sandgum/Triangulate-SF_01-Speaker-Frame/CAD/SF_01 Speaker Frame_STEP/Wall Mounting Piece.step

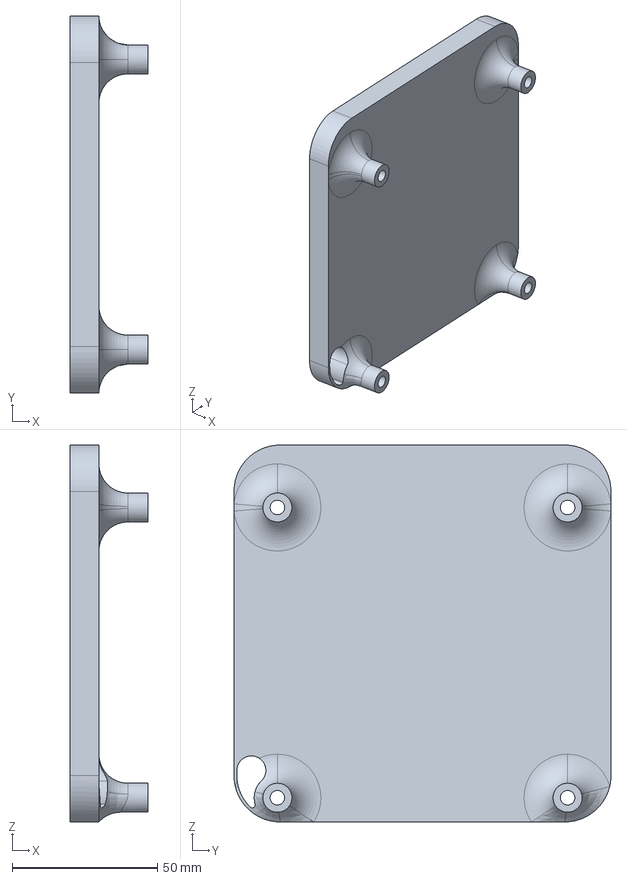
[picture p15: CAD file, 2026-06-28]
CAD/SF_01 Speaker Frame_STEP/Wall Mounting Piece.step
26.9 x 129.9 x 129.9 mm
