sandgum/Triangulate-SF_01-Speaker-Frame/PCB V1.1/PCB Components/TPS54540DDAR Model by Texas Instruments/TPS54540DDAR.step

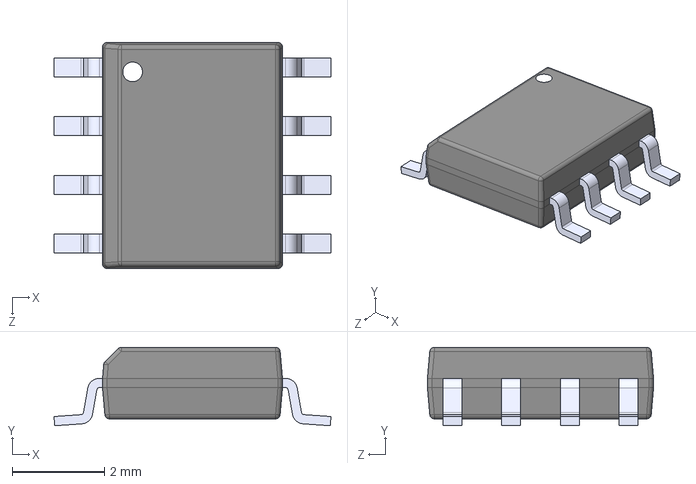
[picture p16: CAD file, 2026-08-03]
PCB V1.1/PCB Components/TPS54540DDAR Model by Texas Instruments/TPS54540DDAR.step
6.00 x 1.70 x 4.90 mm
