sandgum/Triangulate-SF_01-Speaker-Frame/PCB V1.1/PCB Components/JS202011JCQN 3D Model STEP 1.STEP

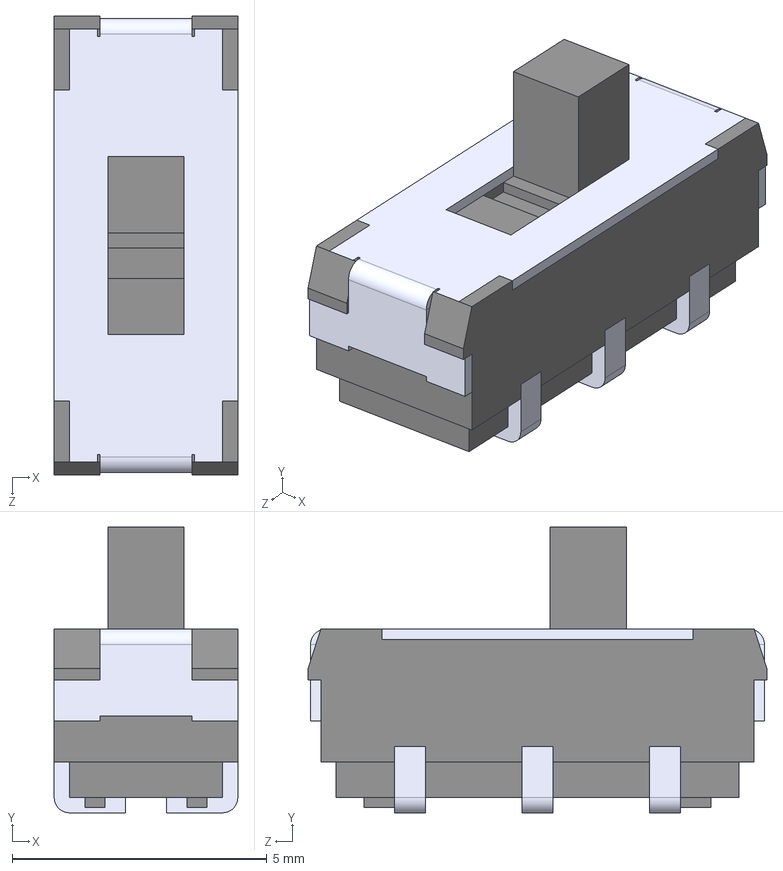
[picture p17: CAD file, 2026-06-28]
PCB V1.1/PCB Components/JS202011JCQN 3D Model STEP 1.STEP
3.60 x 5.60 x 9.00 mm
